chof747/kitchen-clock/3dmodel/components/1.8_inches_128x160_RGB_TFT_LCD v3.step

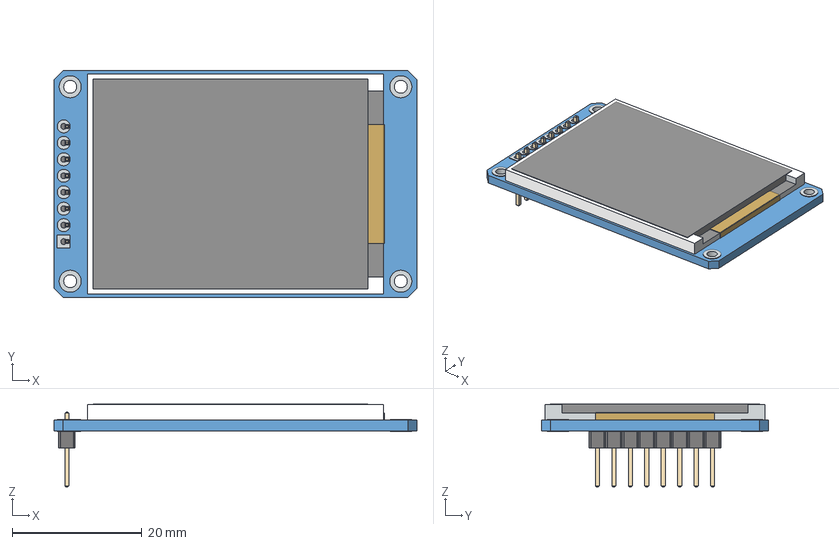
[picture p3: CAD file, 2024-05-20]
3dmodel/components/1.8_inches_128x160_RGB_TFT_LCD v3.step
56.0 x 35.0 x 12.8 mm
Display Board
